alekf-hls/quiz-bowl-buzzer/design/wiring-diagram.png

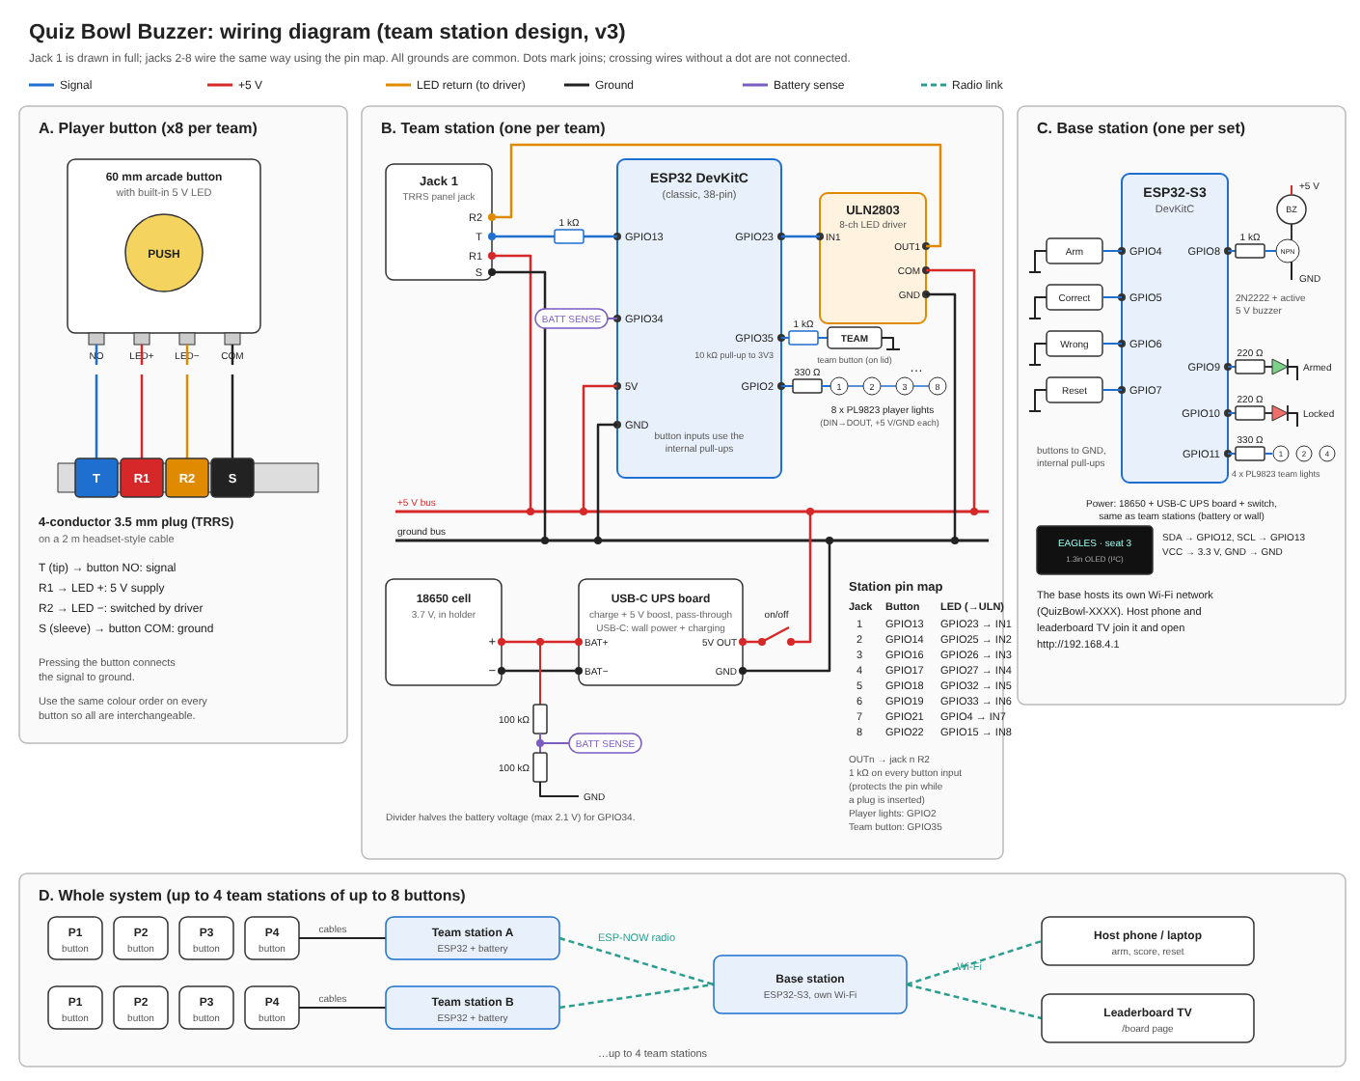
design/wiring-diagram.png
