alekf-hls/quiz-bowl-buzzer/enclosures/preview/base_station_assembly.png

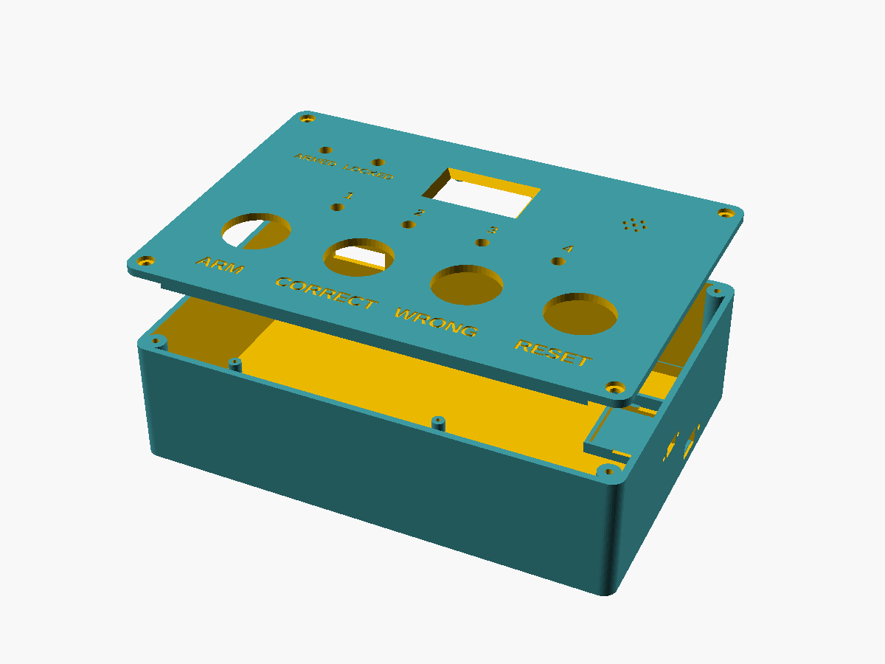
enclosures/preview/base_station_assembly.png
