alekf-hls/quiz-bowl-buzzer/enclosures/preview/team_station_assembly.png

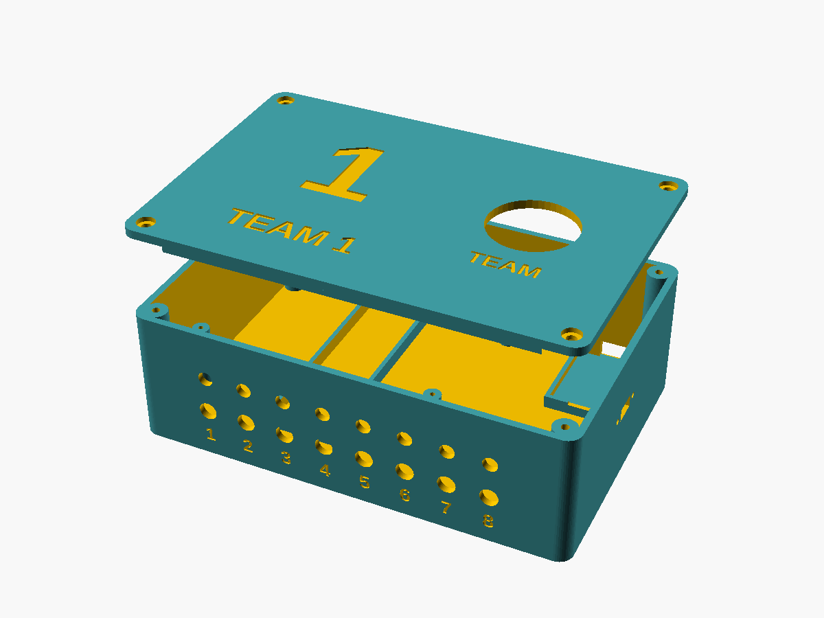
enclosures/preview/team_station_assembly.png
